Blinkinlabs/PovPlayer/documentation/DSC_8254.jpg

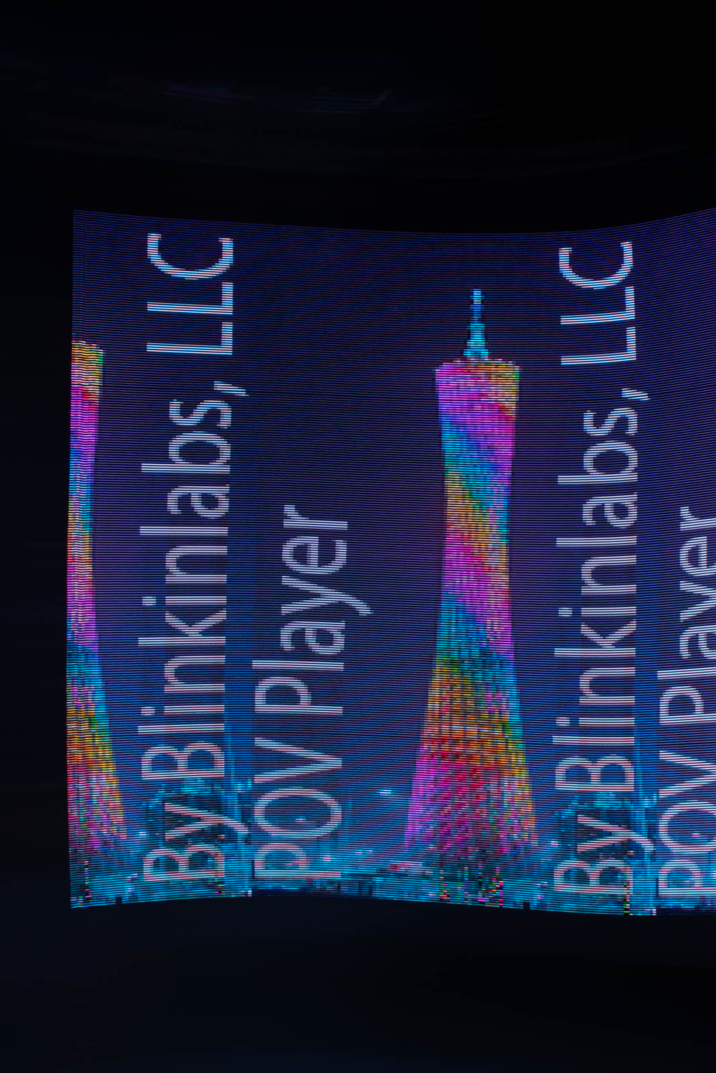
documentation/DSC_8254.jpg
