Blinkinlabs/PovPlayer/documentation/DSC_8299-2.jpg

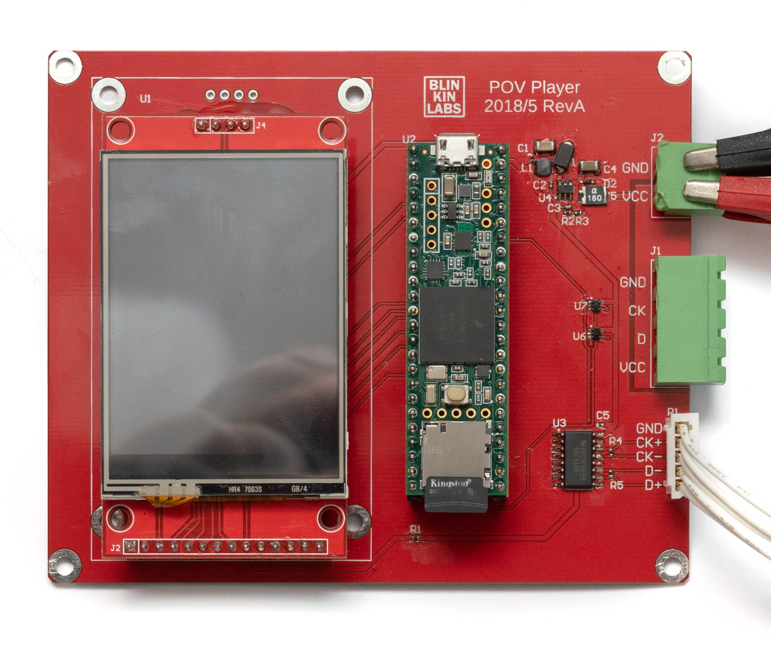
documentation/DSC_8299-2.jpg
