Blinkinlabs/PovPlayer/documentation/DSC_8299.jpg

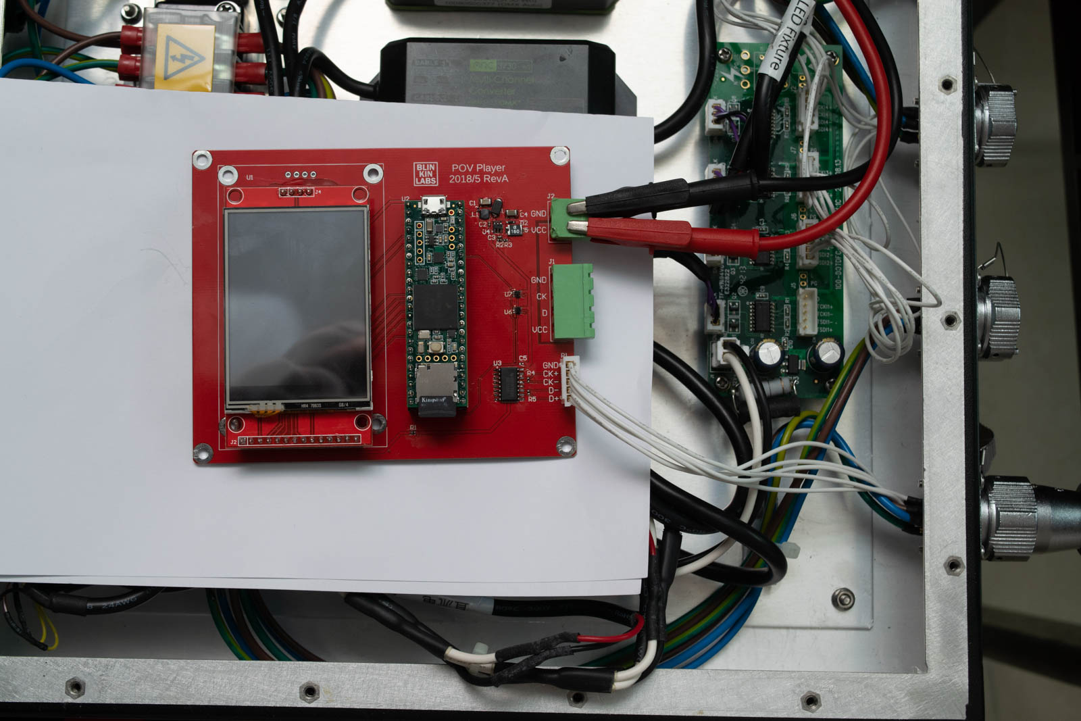
documentation/DSC_8299.jpg
