Blinkinlabs/PovPlayer/sample images/tower.bmp

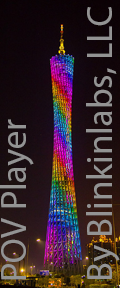
sample images/tower.bmp
