Blinkinlabs/PovPlayer/instructions/2. Select save as.PNG

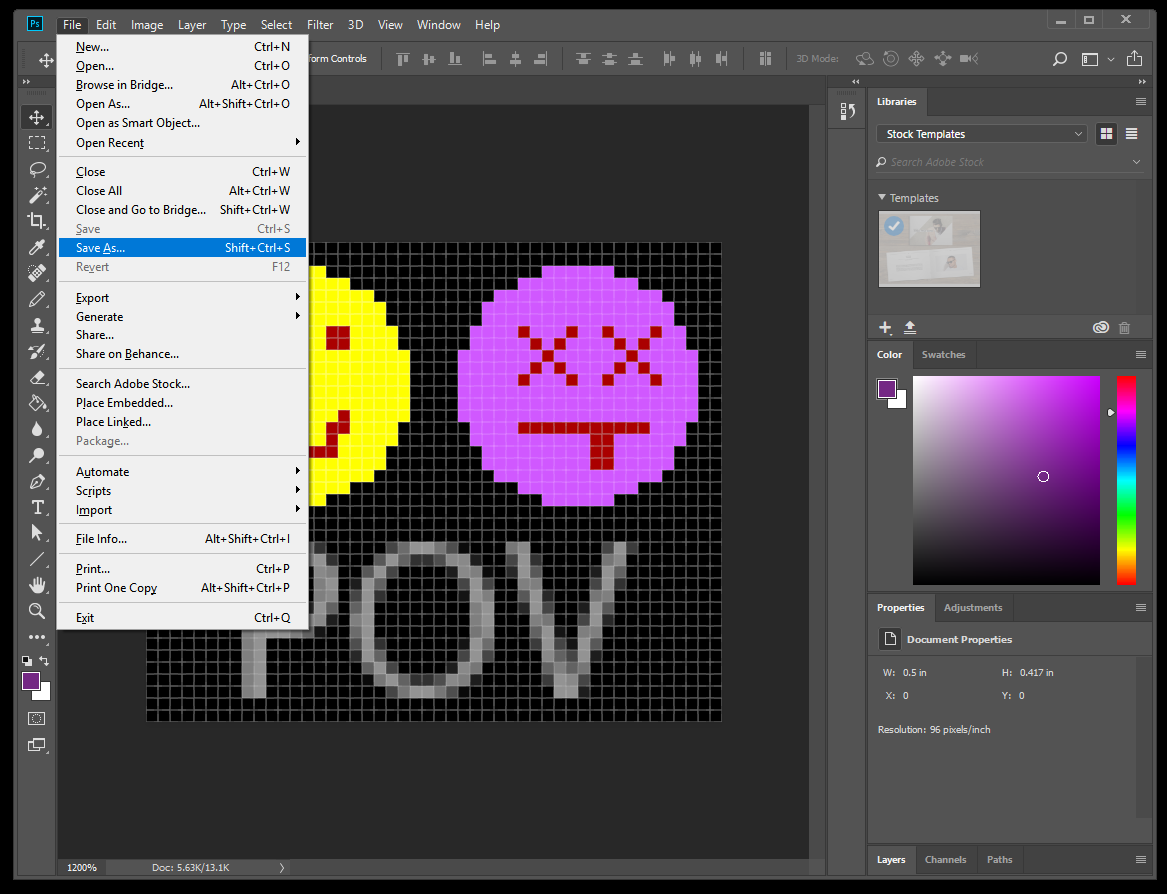
instructions/2. Select save as.PNG
