Blinkinlabs/PovPlayer/instructions/4. Change the name to 'pov.bmp', and click save.PNG

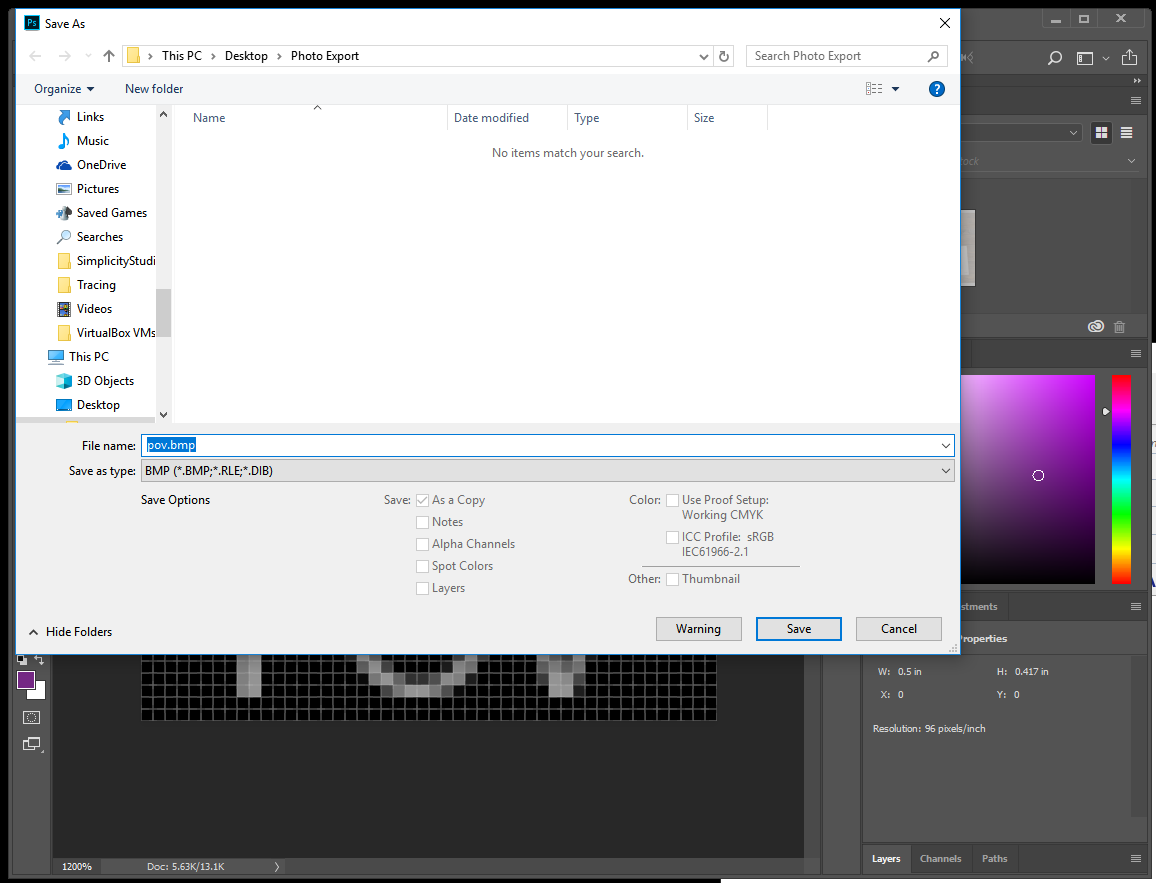
instructions/4. Change the name to 'pov.bmp', and click save.PNG
