Blinkinlabs/PovPlayer/SPI_POV/APA102.h

// APA102.h: Driver for controlling strings of MBI6020 pixel LEDs.
// 2018 Blinkinlabs, LLC

#ifndef APA102_H_
#define APA102_H_

//#include "LED_DATA.h"

const int SPI_CLOCK_FREQ = 10000000;

extern void apa102_begin(size_t count, int spiClockFrequency);

extern void apa102_SendData(const uint8_t * data, size_t count, int spiClockFrequency);

#endif
